DAI-Maker-Lab/tepmachcha/photos/P1-P3_pads.JPG

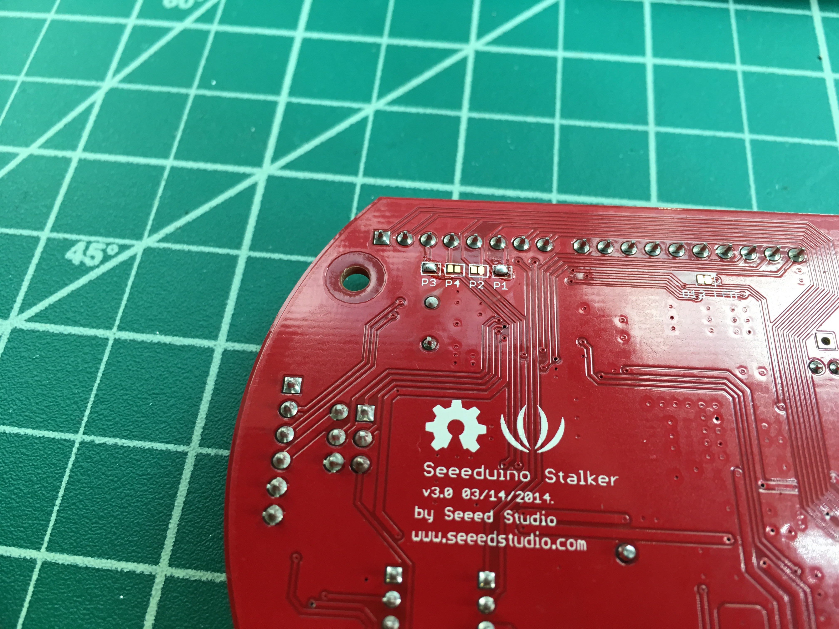
photos/P1-P3_pads.JPG
