DAI-Maker-Lab/tepmachcha/photos/spacers_interior.JPG

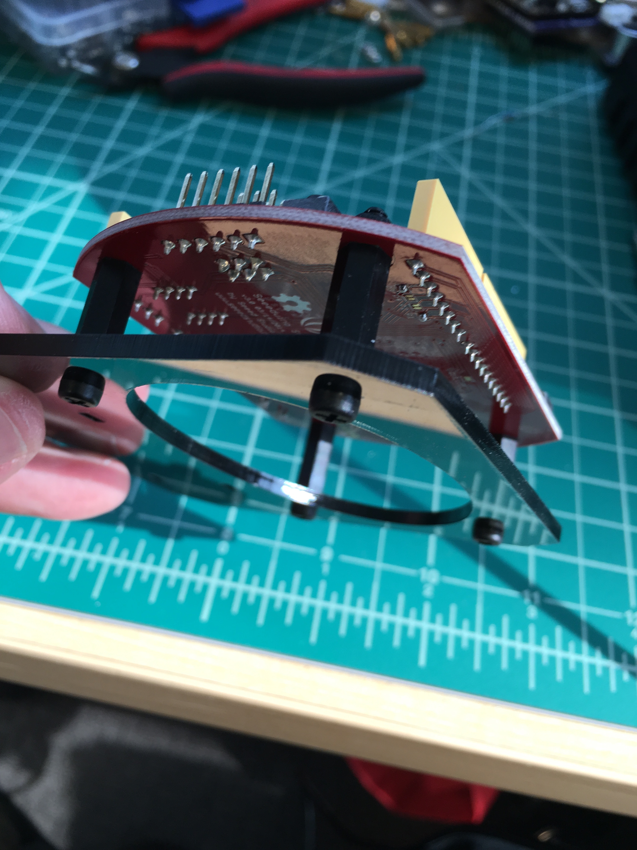
photos/spacers_interior.JPG
