DAI-Maker-Lab/tepmachcha/photos/splice.JPG

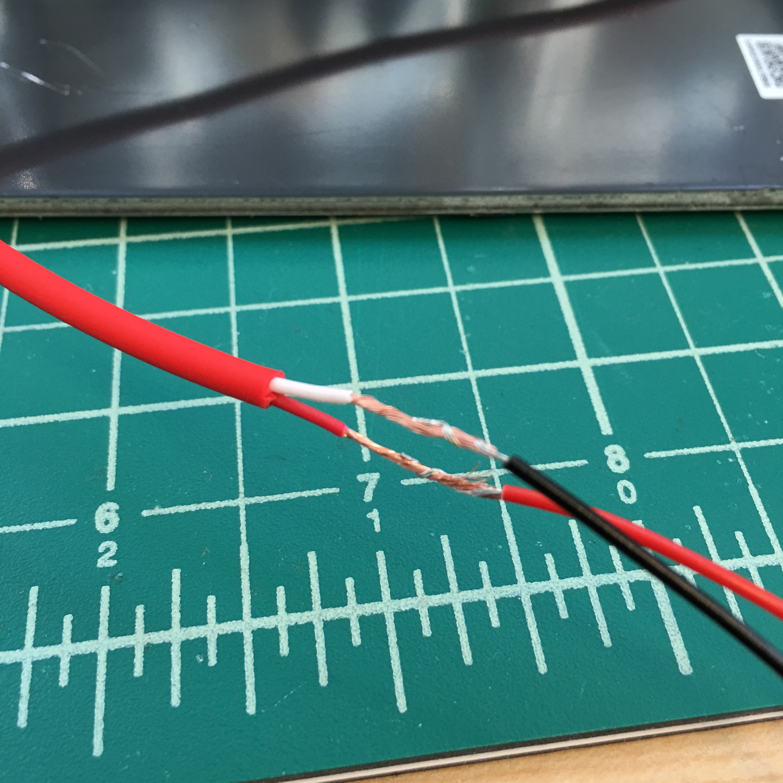
photos/splice.JPG
