DAI-Maker-Lab/tepmachcha/photos/sonar_solder.JPG

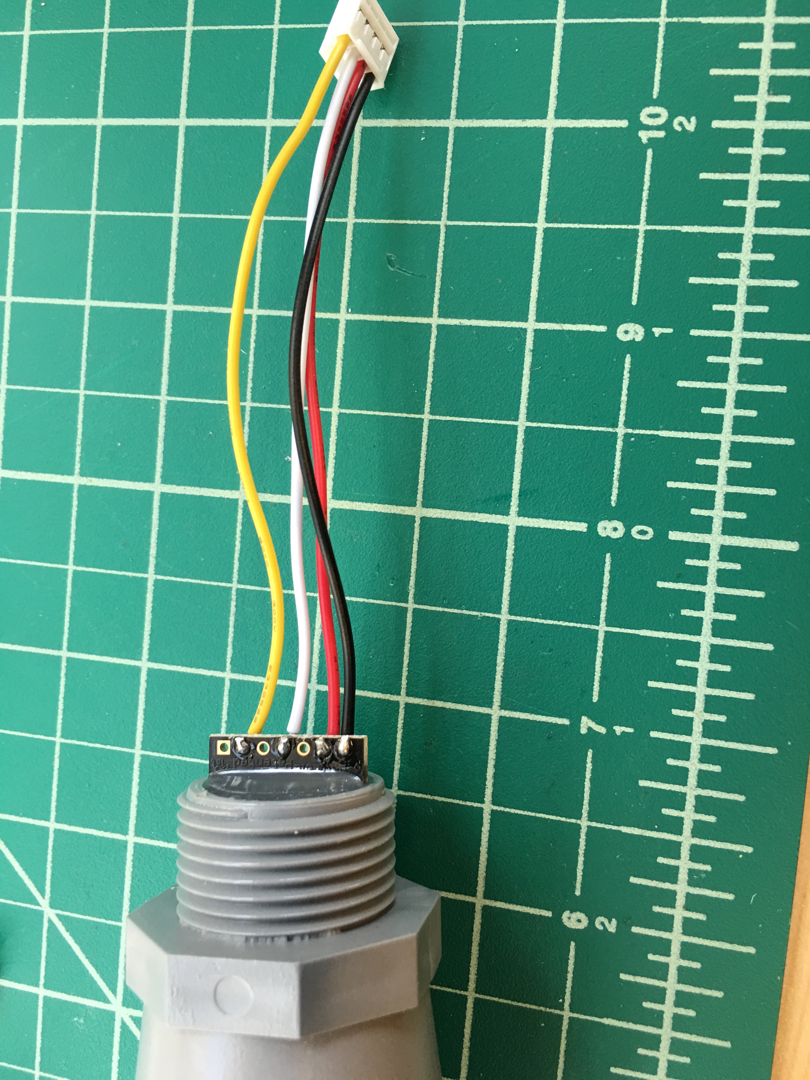
photos/sonar_solder.JPG
